svenpetersen1965/PET-Joystick-Adapter/Case/Rev. 0/Label/Label.png

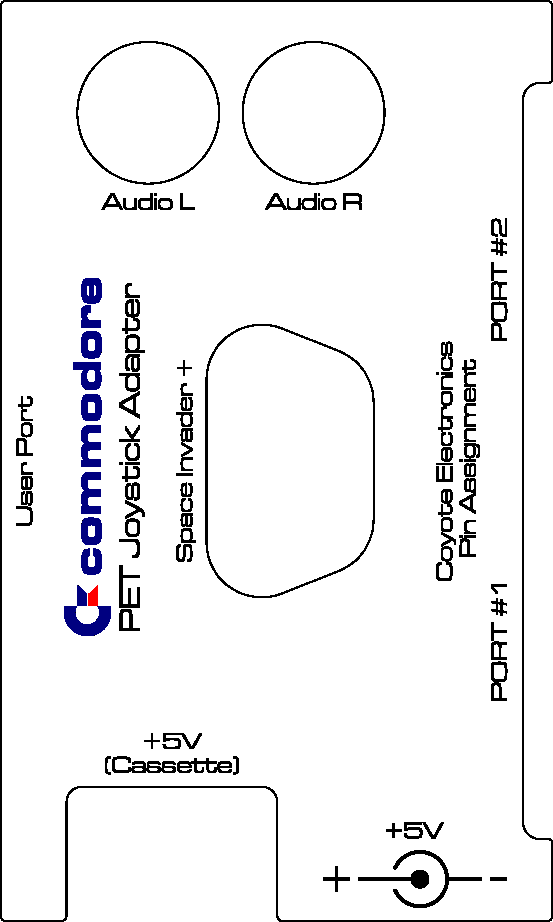
Case/Rev. 0/Label/Label.png
