svenpetersen1965/PET-Joystick-Adapter/Rev. 0/pictures/IMG_0694.JPG

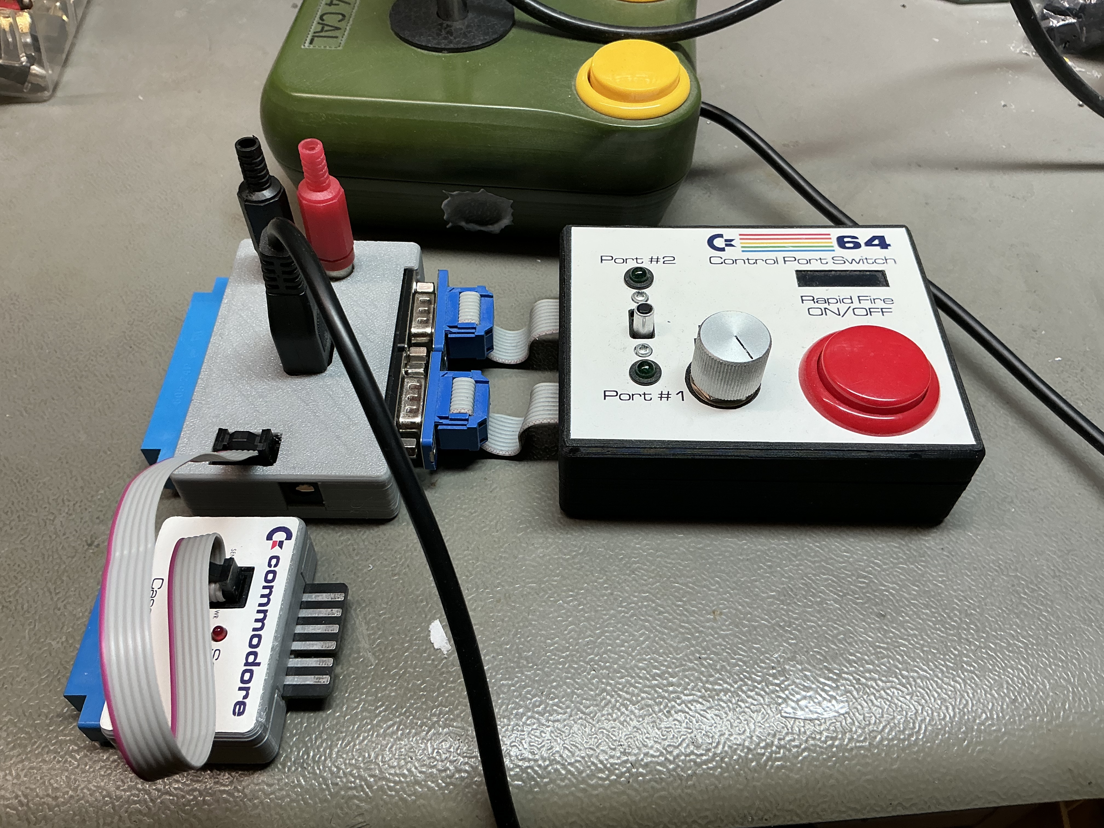
Rev. 0/pictures/IMG_0694.JPG
