svenpetersen1965/PET-Joystick-Adapter/Rev. 0/pictures/IMG_0710.JPG

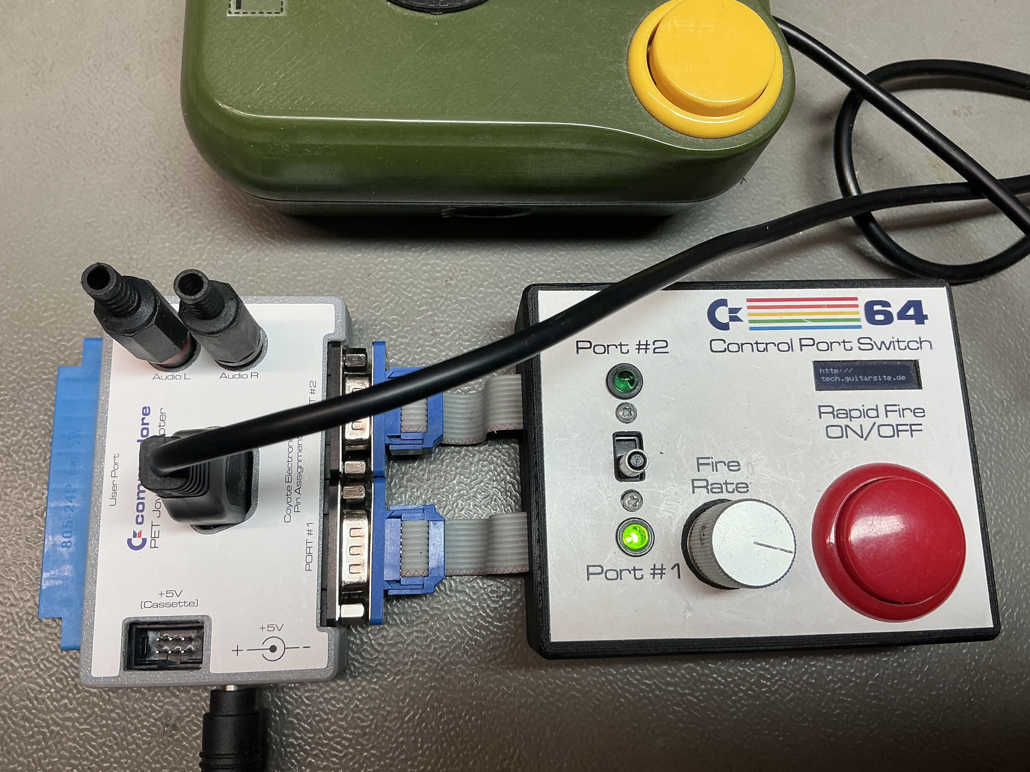
Rev. 0/pictures/IMG_0710.JPG
